nathab32/ESP32-IoT-Clock/src/Sensitive.h

#define APP_KEY "xxxxxxxxxxxxxx"     // Should look like "de0bxxxx-1x3x-4x3x-ax2x-5dabxxxxxxxx"
#define APP_SECRET "xxxxxxxxxxxxxx"  // Should look like "5f36xxxx-x3x7-4x3x-xexe-e86724a9xxxx-4c4axxxx-3x3x-x5xe-x9x3-333d65xxxxxx"
#define TEMP_ID "xxxxxxxxxxxxxx"     // Should look like "5dc1564130xxxxxxxxxxxxxx"
#define SWITCH_ID "xxxxxxxxxxxxxx"
#define LIGHT_ID "xxxxxxxxxxxxxx"

// Fill with own WiFi credentials
const String SSID[] = {
    "xxxxxxxxxxxxxx",
    "xxxxxxxxxxxxxx",
    "xxxxxxxxxxxxxx",
    "xxxxxxxxxxxxxx"
};

const String PASS[] = {
    "xxxxxxxxxxxxxx",
    "xxxxxxxxxxxxxx",
    "xxxxxxxxxxxxxx",
    "xxxxxxxxxxxxxx"
};
